Aryan-G4/AIR.C---Autonomous-Infrared-Camera/Transmitter/MLX_Arduino_integration/main/main.c

#include <stdio.h>
#include "Arduino.h"

/*Things to change from the example code to make this work:

1. Change any "serial. functions (i.e Serial.begin and Serial.println) to printf() or Uart transmission"app_main
2. Remove void startup() and void loop() and instead put them into void app_main() with a while(1) loop.app_main

*/
void app_main(void)
{
    pinMode(2,OUTPUT);

    while(1){
        digitalWrite(2,1);
        delay(1000);
    }
}
