Aryan-G4/AIR.C---Autonomous-Infrared-Camera/Transmitter/project-name/main/wireless_esp.h

#ifndef WIRELESS_ESP_H
#define WIRELESS_ESP_H

#include "main.h"  // Include main.h to use print_msg()
#include <esp_wifi.h>
// Function Declarations
void wirelessmessagetest();
void read_mac_address();
void wifi_init();

#endif // WIRELESS_ESP_H
